ihackurass/QoriPunku/Imagenes/battery.jpg

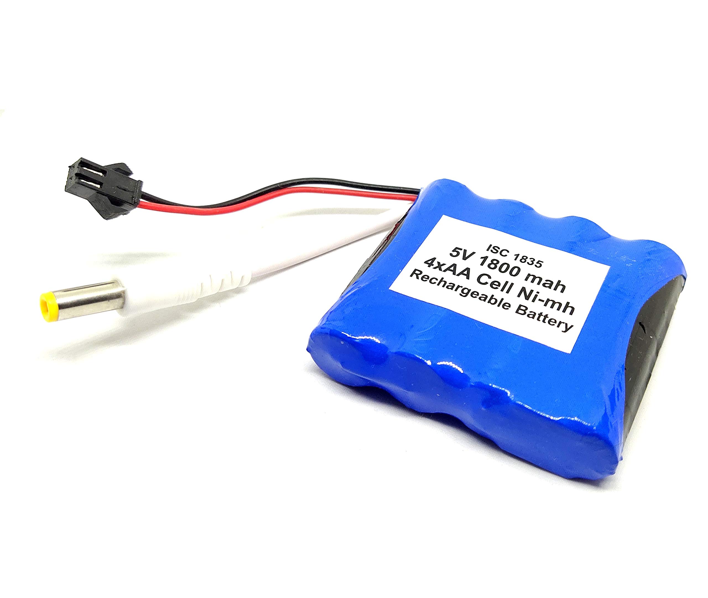
Imagenes/battery.jpg
