ihackurass/QoriPunku/Imagenes/i2c.jpg

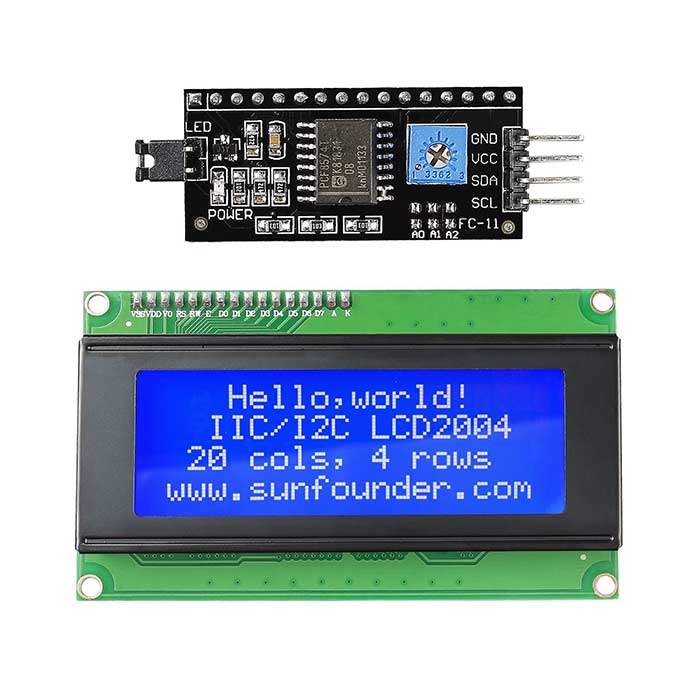
Imagenes/i2c.jpg
