ihackurass/QoriPunku/Web/whatsapp/Fotos/images_1.png

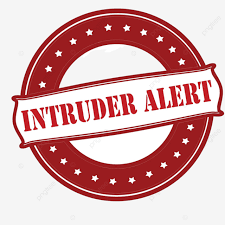
Web/whatsapp/Fotos/images_1.png
